codetit4n/nrf52840-capacitance-meter/docs/architecture.kicad_sch

## KiCad design docs/architecture.kicad_sch (2026-09-15)

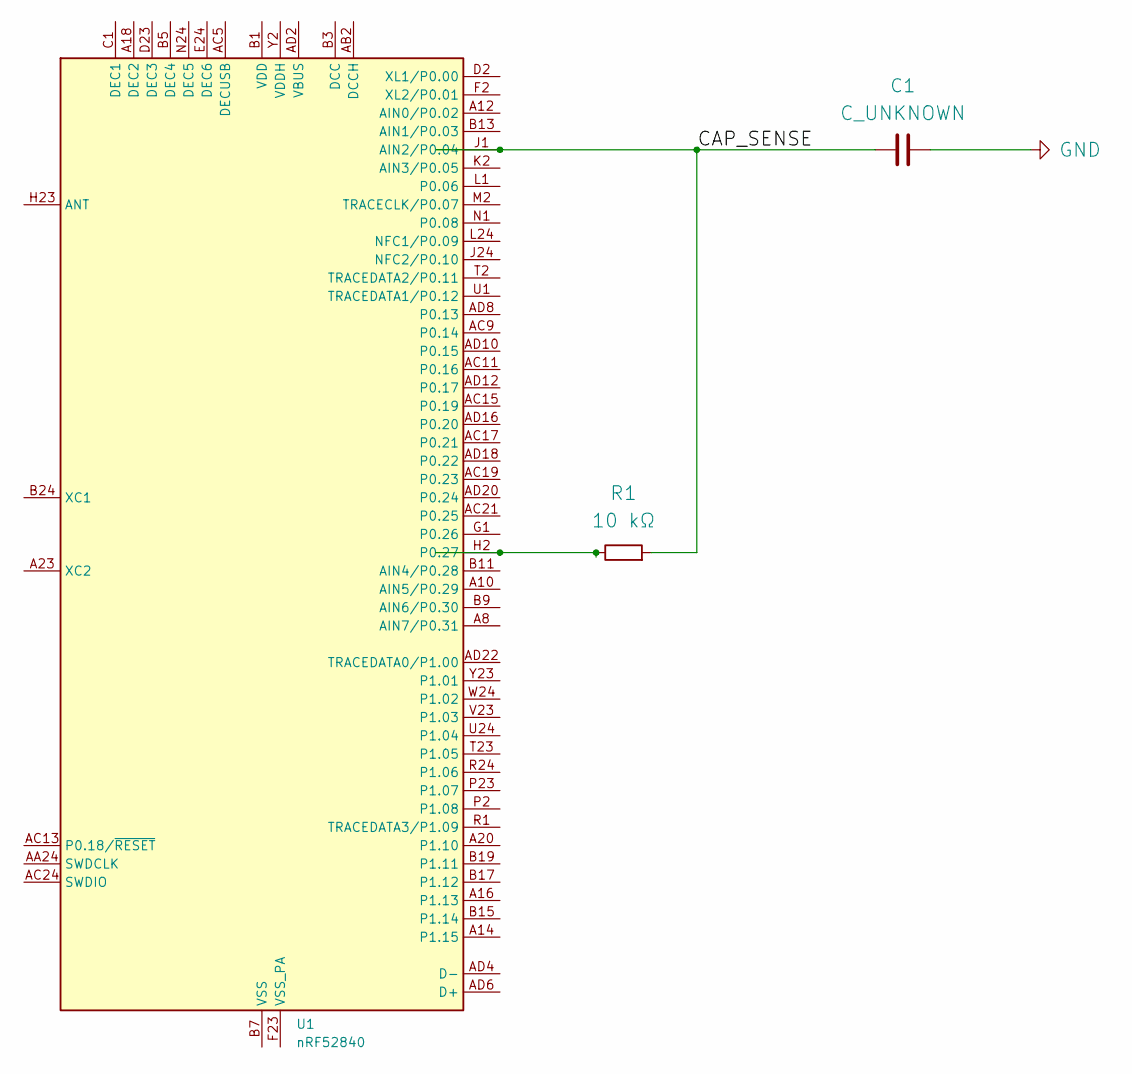
[picture p7: schematic architecture.kicad_sch]

Parts:
C1: C_UNKNOWN; WDFN-10-1EP_3x3mm_P0.5mm_EP1.8x2.5mm
R1: 10 kΩ; R_Array_SIP4
U1: nRF52840; Nordic_AQFN-73-1EP_7x7mm_P0.5mm

Connections:
CAP_SENSE: C1.1, R1.2, U1.J1 (AIN2/P0.04)
GND: C1.2
unnamed: R1.1, U1.H2 (P0.27)
unnamed: U1.A22 (VDD), U1.AD14 (VDD), U1.AD23 (VDD), U1.B1 (VDD), U1.W1 (VDD)
unnamed: U1.B7 (VSS), U1.EP (VSS)
