codetit4n/nrf52840-capacitance-meter/include/timer.h

#include <stdint.h>

#define NRF_TIMER0_BASE 0x40008000UL

#define TIMER_MODE_REG REG32(NRF_TIMER0_BASE + 0x504)
#define TIMER_BITMODE_REG REG32(NRF_TIMER0_BASE + 0x508)
#define TIMER_CC0_REG REG32(NRF_TIMER0_BASE + 0x540)
#define TIMER_PRESCALER_REG REG32(NRF_TIMER0_BASE + 0x510)

#define TIMER_TASKS_START_REG REG32(NRF_TIMER0_BASE + 0x000)
#define TIMER_TASKS_STOP_REG REG32(NRF_TIMER0_BASE + 0x004)
#define TIMER_TASKS_CLEAR_REG REG32(NRF_TIMER0_BASE + 0x00C)
#define TIMER_TASKS_CAPTURE0_REG REG32(NRF_TIMER0_BASE + 0x040)

void init_timer0(void);
void clear_ctr_and_start_timer(void);
uint32_t stop_timer_and_read_ctr(void);
