codetit4n/nrf52840-capacitance-meter/include/adc.h

#include <stdint.h>

#define NRF_SAADC_BASE 0x40007000UL

// for Channel 0 only
#define ADC_PSELP_REG REG32(NRF_SAADC_BASE + 0x510) // for P0.04
#define ADC_CONFIG_REG REG32(NRF_SAADC_BASE + 0x518)
#define ADC_ENABLE_REG REG32(NRF_SAADC_BASE + 0x500)
#define ADC_RESOLUTION_REG REG32(NRF_SAADC_BASE + 0x5F0)
#define ADC_TASKS_START_REG REG32(NRF_SAADC_BASE + 0x000)
#define ADC_TASKS_SAMPLE_REG REG32(NRF_SAADC_BASE + 0x004)
#define ADC_TASKS_STOP_REG REG32(NRF_SAADC_BASE + 0x008)

#define ADC_EVENTS_STARTED_REG REG32(NRF_SAADC_BASE + 0x100)
#define ADC_EVENTS_END_REG REG32(NRF_SAADC_BASE + 0x104)
#define ADC_EVENTS_DONE_REG REG32(NRF_SAADC_BASE + 0x108)

#define ADC_RESULT_PTR_REG REG32(NRF_SAADC_BASE + 0x62C)
#define ADC_RESULT_MAXCNT_REG REG32(NRF_SAADC_BASE + 0x630)

void init_saadc0(void);
uint32_t saadc_read(void);
